jeffmerrick/typeframe/ps-85/software/images/nostromo-boot.png

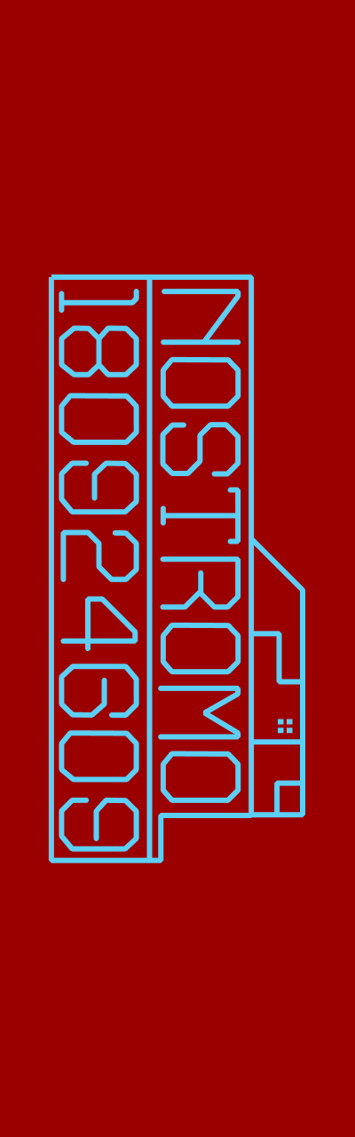
ps-85/software/images/nostromo-boot.png
