jeffmerrick/typeframe/px-88/software/images/typeframe-boot-simple.png

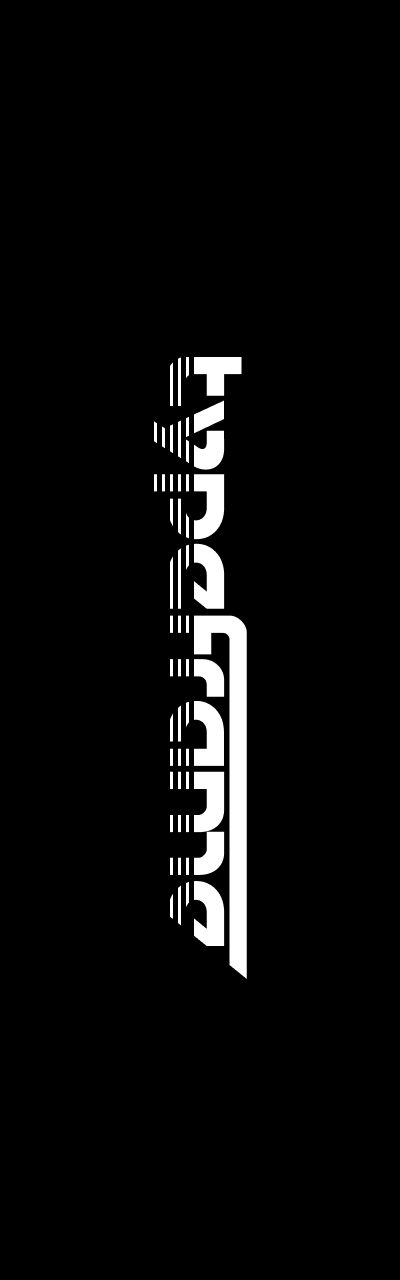
px-88/software/images/typeframe-boot-simple.png
