jeffmerrick/typeframe/website/docs/ps-85/img/typeframe-ps-85-02.jpg

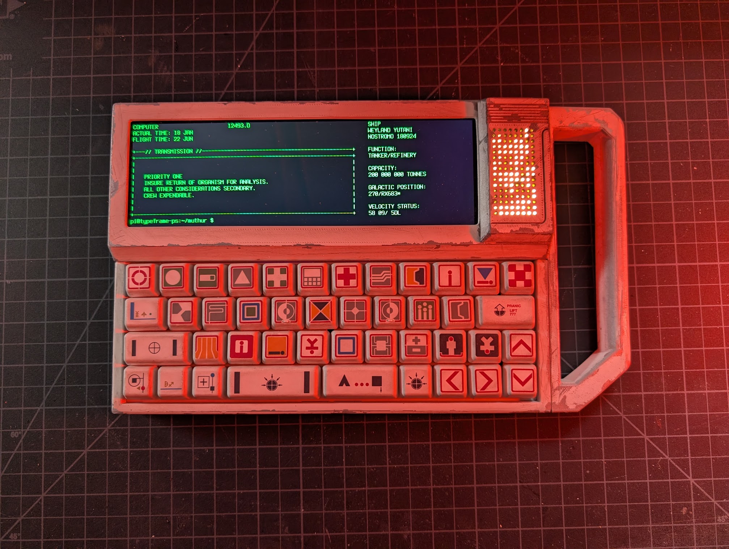
website/docs/ps-85/img/typeframe-ps-85-02.jpg
