jeffmerrick/typeframe/website/docs/ps-85/img/typeframe-ps-85-08.jpg

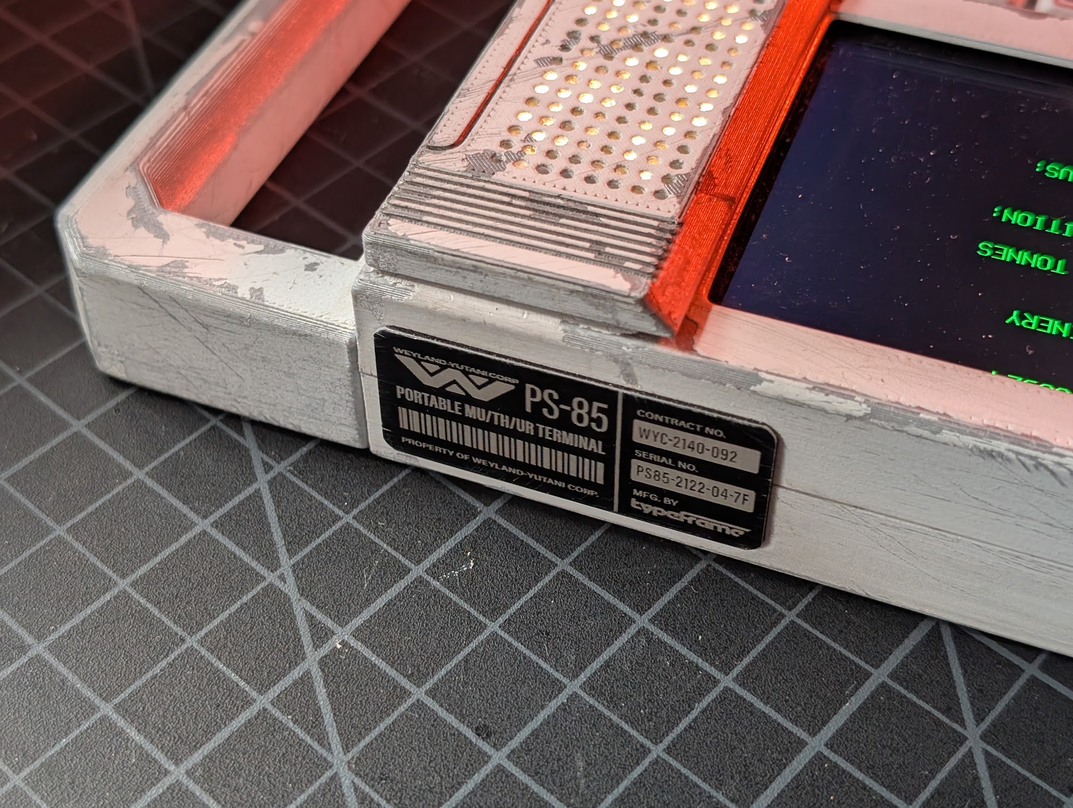
website/docs/ps-85/img/typeframe-ps-85-08.jpg
