jeffmerrick/typeframe/website/docs/px-88/img/typeframe-px-88-06.jpg

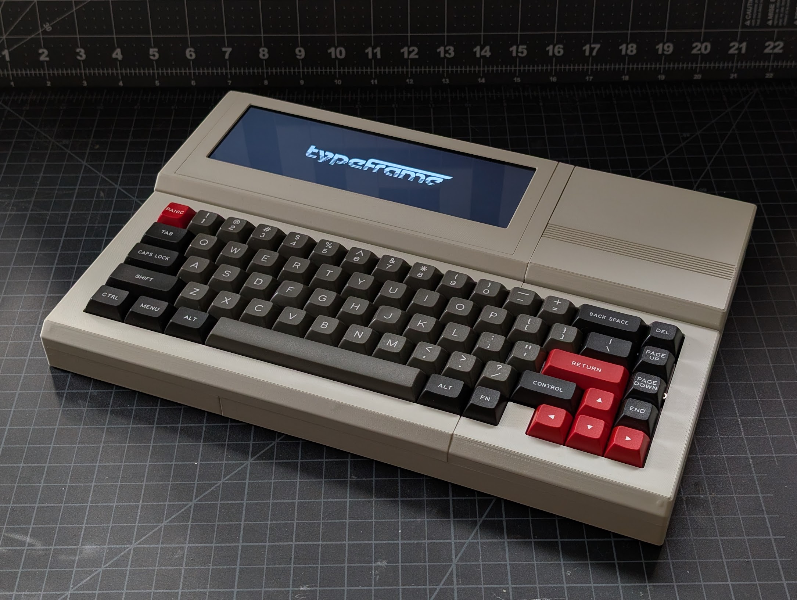
website/docs/px-88/img/typeframe-px-88-06.jpg
