jeffmerrick/typeframe/website/docs/px-88/img/typeframe-px-88-paul-2.jpg

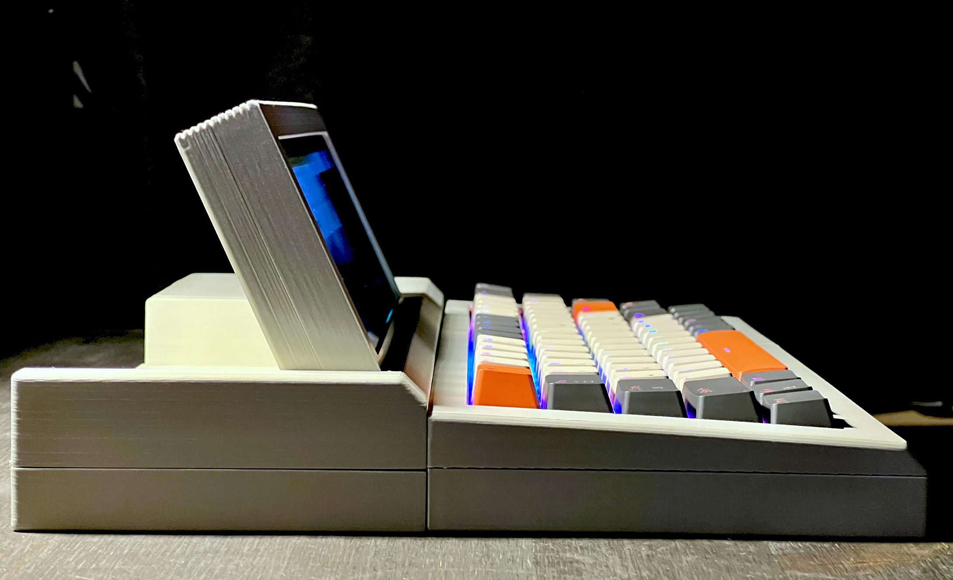
website/docs/px-88/img/typeframe-px-88-paul-2.jpg
