jeffmerrick/typeframe/website/docs/px-88/img/typeframe-px-88-paul-3.jpg

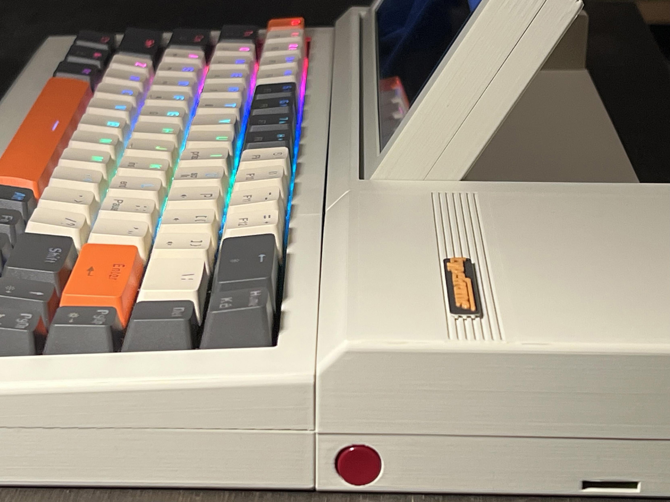
website/docs/px-88/img/typeframe-px-88-paul-3.jpg
