jeffmerrick/typeframe/website/src/pages/img/typeframe-ps-85-hero-simple.png

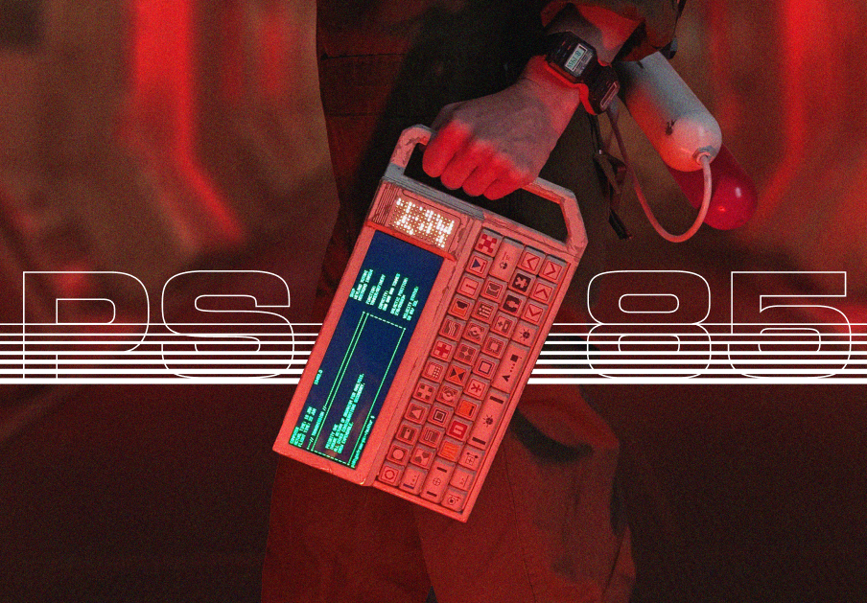
website/src/pages/img/typeframe-ps-85-hero-simple.png
