jeffmerrick/typeframe/website/src/pages/img/typeframe-ps-85-hero.png

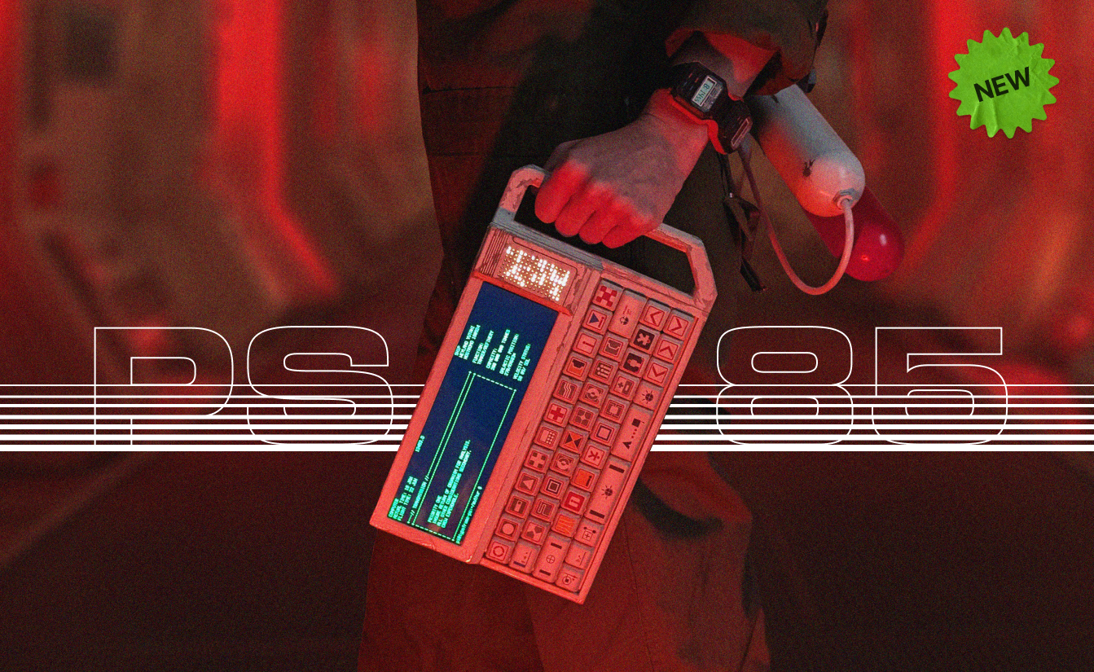
website/src/pages/img/typeframe-ps-85-hero.png
