jeffmerrick/typeframe/website/src/pages/img/typeframe-px-88-hero-simple.png

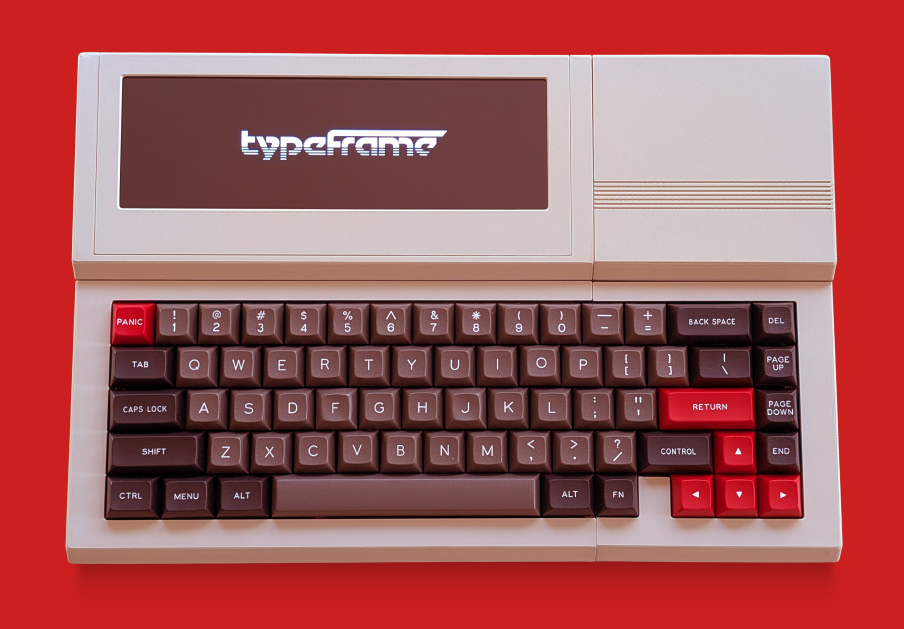
website/src/pages/img/typeframe-px-88-hero-simple.png
