jeffmerrick/typeframe/website/src/pages/img/typeframe-px-88-hero.png

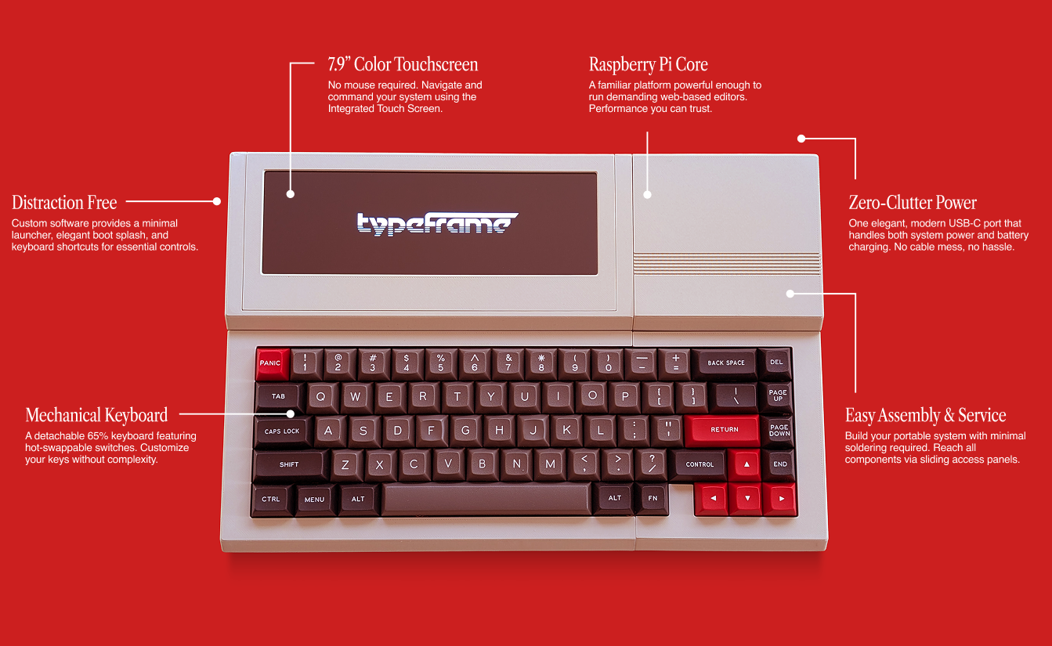
website/src/pages/img/typeframe-px-88-hero.png
