jeffmerrick/typeframe/px-88/hardware/print-files/tight-tolerances/STL/hinge_shaft_x2_0.05mm.stl

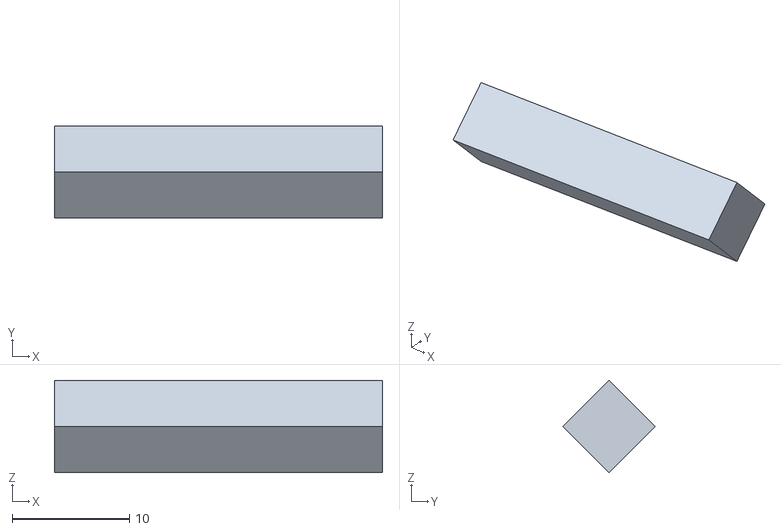
[picture p51: CAD file, 2025-11-28]
px-88/hardware/print-files/tight-tolerances/STL/hinge_shaft_x2_0.05mm.stl
28.0 x 7.86 x 7.86
