jeffmerrick/typeframe/ps-85/hardware/print-files/STL/keyboard_plate.stl

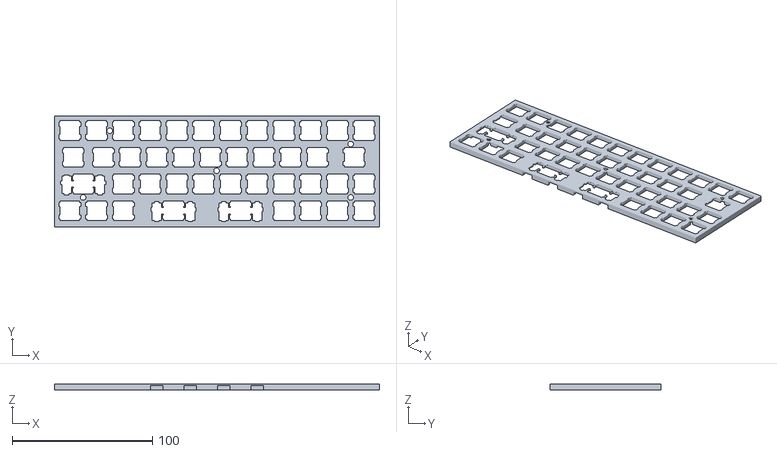
[picture p52: CAD file, 2026-01-20]
ps-85/hardware/print-files/STL/keyboard_plate.stl
231.4 x 78.8 x 4.40
