jeffmerrick/typeframe/px-88/hardware/print-files/loose-tolerances/STL/keyboard_case_top_right.stl

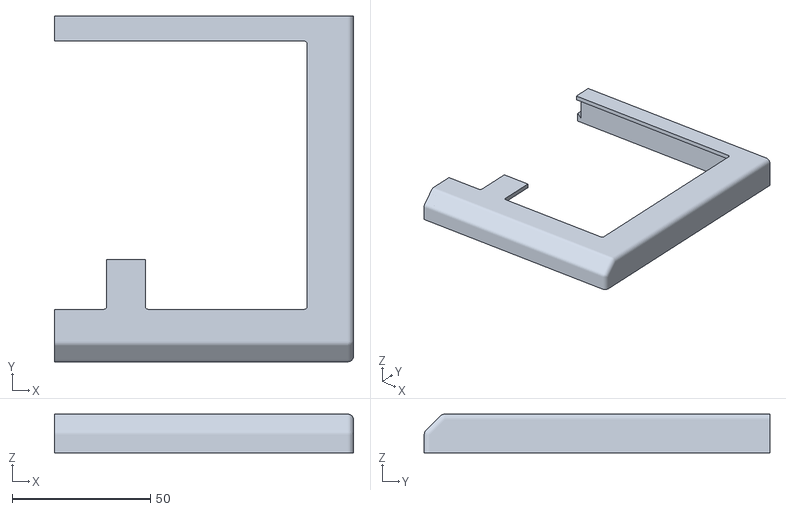
[picture p53: CAD file, 2025-12-03]
px-88/hardware/print-files/loose-tolerances/STL/keyboard_case_top_right.stl
108.1 x 125.0 x 14.0
