jeffmerrick/typeframe/px-88/hardware/print-files/tight-tolerances/3MF/keyboard_case.3mf

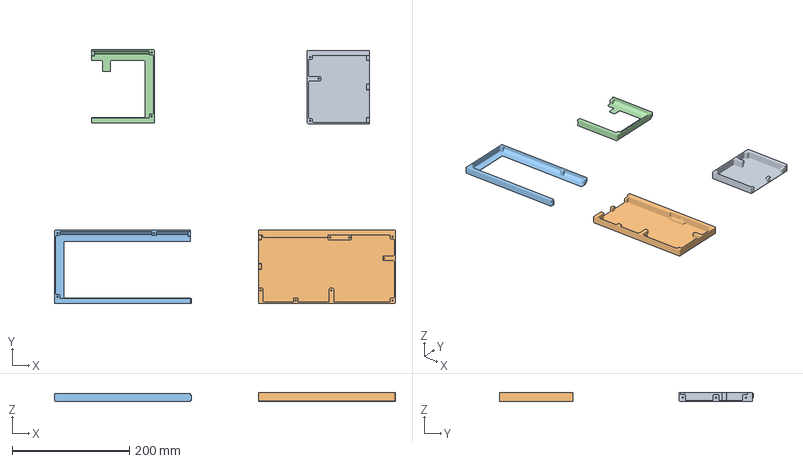
[picture p54: CAD file, 2025-11-03]
px-88/hardware/print-files/tight-tolerances/3MF/keyboard_case.3mf
581.8 x 432.9 x 16.0 mm
keyboard case bottom left
keyboard case bottom right
keyboard case top left
keyboard case top right
