jeffmerrick/typeframe/ps-85/hardware/print-files/STL/keyboard_top.stl

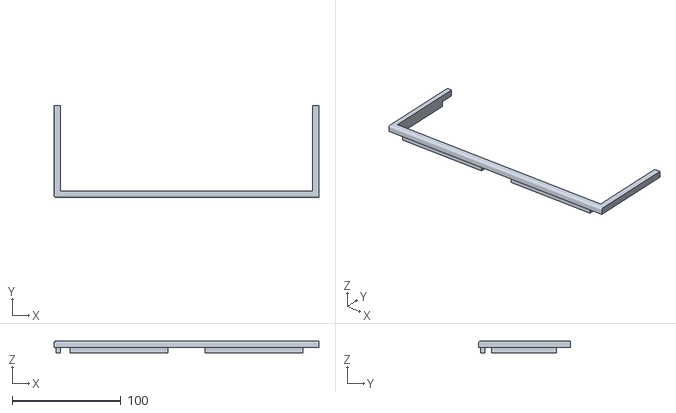
[picture p56: CAD file, 2026-01-20]
ps-85/hardware/print-files/STL/keyboard_top.stl
243.6 x 85.0 x 11.0
