jeffmerrick/typeframe/px-88/hardware/print-files/loose-tolerances/STL/keyboard_case_top_left.stl

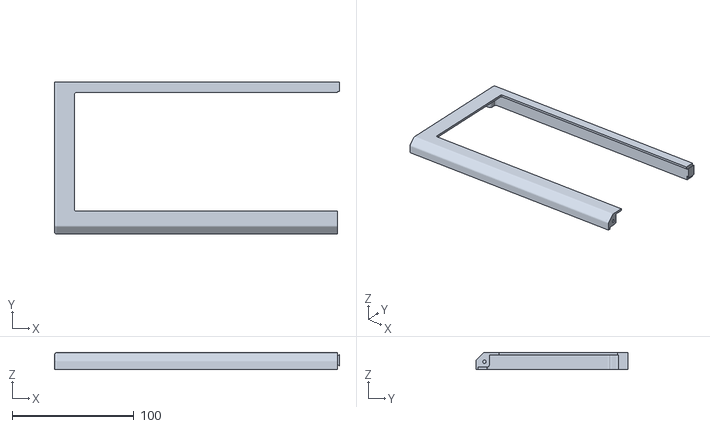
[picture p57: CAD file, 2025-12-03]
px-88/hardware/print-files/loose-tolerances/STL/keyboard_case_top_left.stl
233.6 x 125.0 x 14.0
