jeffmerrick/typeframe/px-88/hardware/print-files/tight-tolerances/STL/hinge_barrel_x2_0.15mm.stl

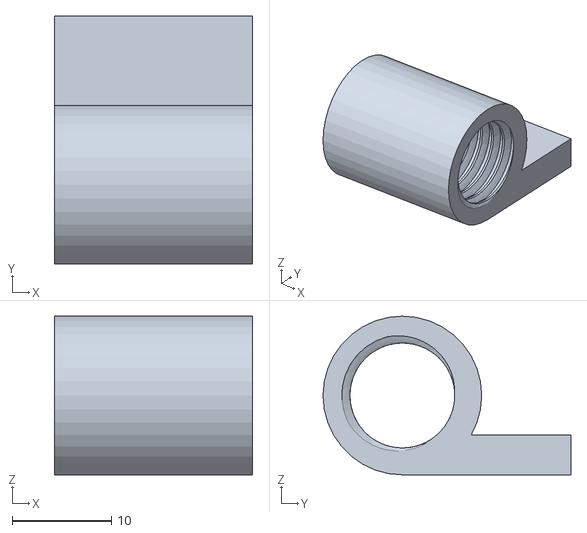
[picture p58: CAD file, 2025-11-28]
px-88/hardware/print-files/tight-tolerances/STL/hinge_barrel_x2_0.15mm.stl
20.0 x 25.0 x 16.0
