jeffmerrick/typeframe/ps-85/hardware/print-files/STL/handle.stl

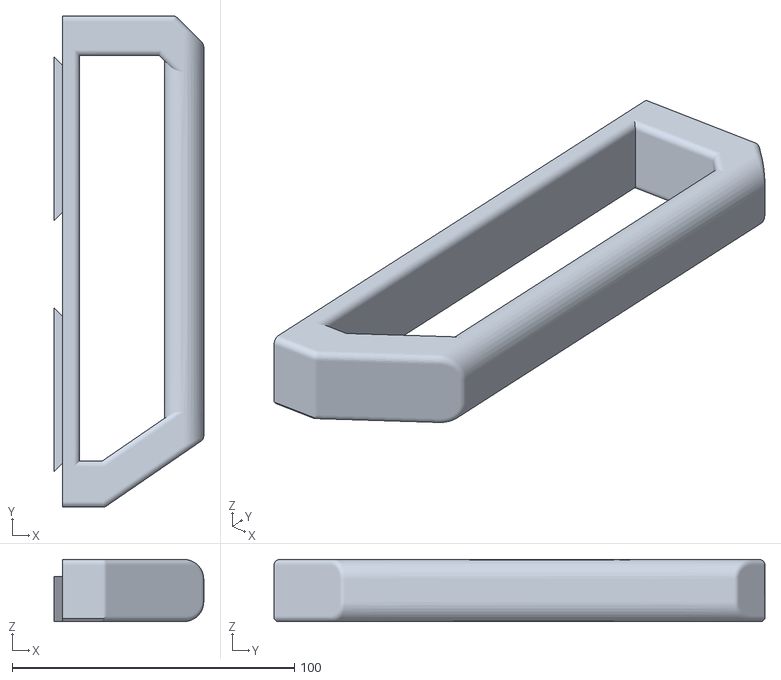
[picture p59: CAD file, 2026-01-20]
ps-85/hardware/print-files/STL/handle.stl
53.0 x 174.0 x 22.0
