jeffmerrick/typeframe/px-88/hardware/print-files/loose-tolerances/STL/screen_bottom.stl

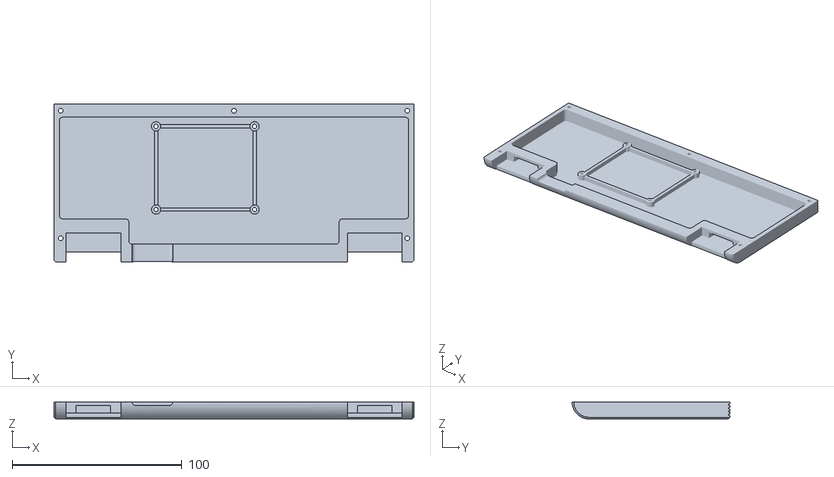
[picture p60: CAD file, 2025-12-03]
px-88/hardware/print-files/loose-tolerances/STL/screen_bottom.stl
212.0 x 93.0 x 10.0
