jeffmerrick/typeframe/px-88/hardware/print-files/tight-tolerances/STL/hinge_slider_x2.stl

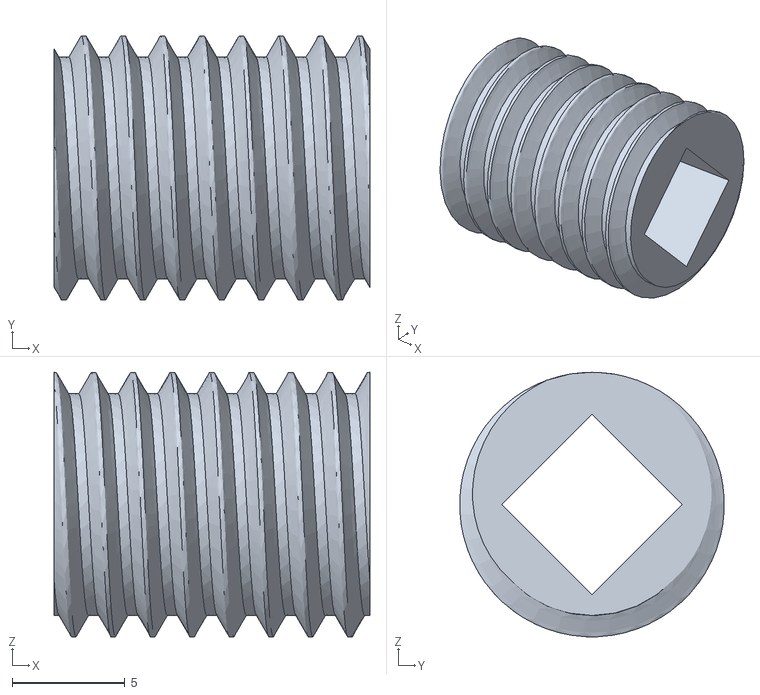
[picture p61: CAD file, 2025-11-28]
px-88/hardware/print-files/tight-tolerances/STL/hinge_slider_x2.stl
14.0 x 11.7 x 11.7
