jeffmerrick/typeframe/ps-85/hardware/print-files/STL/screen_top.stl

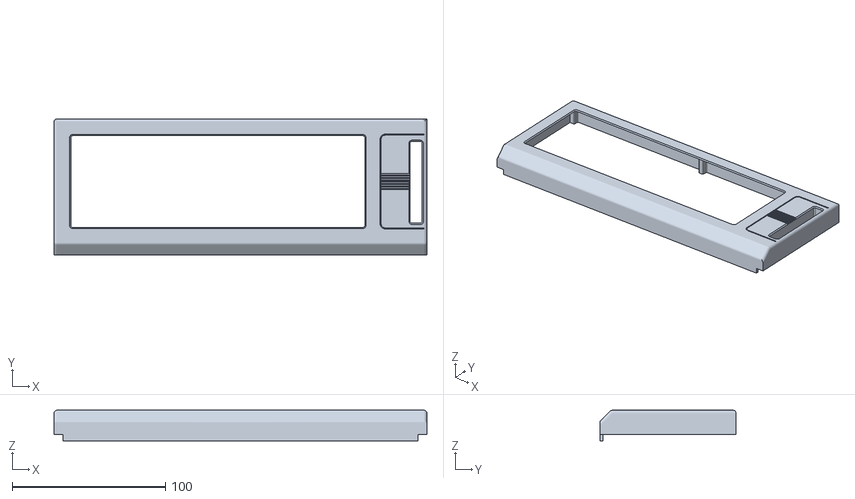
[picture p62: CAD file, 2026-01-20]
ps-85/hardware/print-files/STL/screen_top.stl
243.6 x 89.0 x 20.0
