jeffmerrick/typeframe/px-88/hardware/print-files/loose-tolerances/STL/case_lid.stl

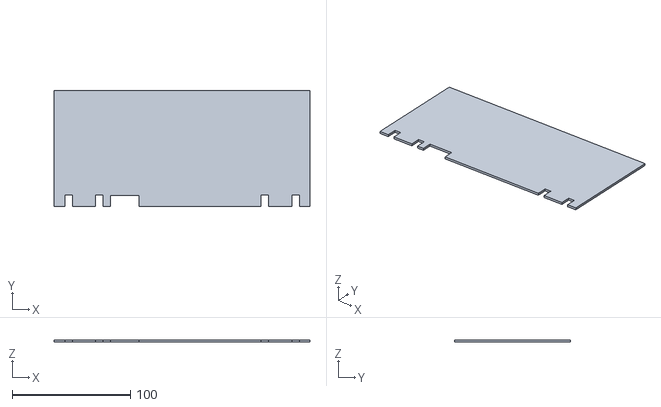
[picture p63: CAD file, 2025-12-03]
px-88/hardware/print-files/loose-tolerances/STL/case_lid.stl
216.1 x 97.9 x 2.00
