jeffmerrick/typeframe/px-88/hardware/print-files/loose-tolerances/STL/keyboard_case_bottom_right.stl

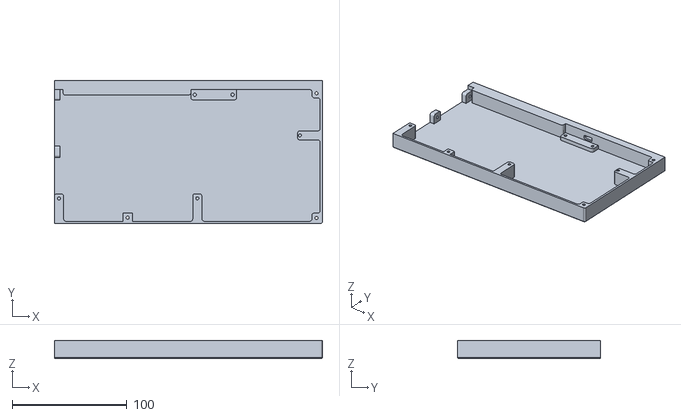
[picture p64: CAD file, 2025-12-03]
px-88/hardware/print-files/loose-tolerances/STL/keyboard_case_bottom_right.stl
234.0 x 125.0 x 16.0
