jeffmerrick/typeframe/px-88/hardware/print-files/loose-tolerances/STL/screen_top.stl

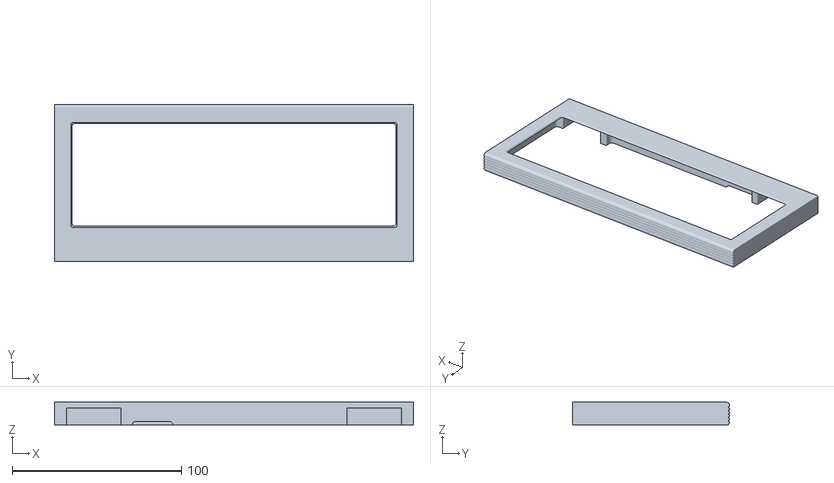
[picture p65: CAD file, 2025-12-03]
px-88/hardware/print-files/loose-tolerances/STL/screen_top.stl
212.0 x 93.0 x 13.4
