jeffmerrick/typeframe/px-88/hardware/print-files/tight-tolerances/STL/hinge_cap_right_x2.stl

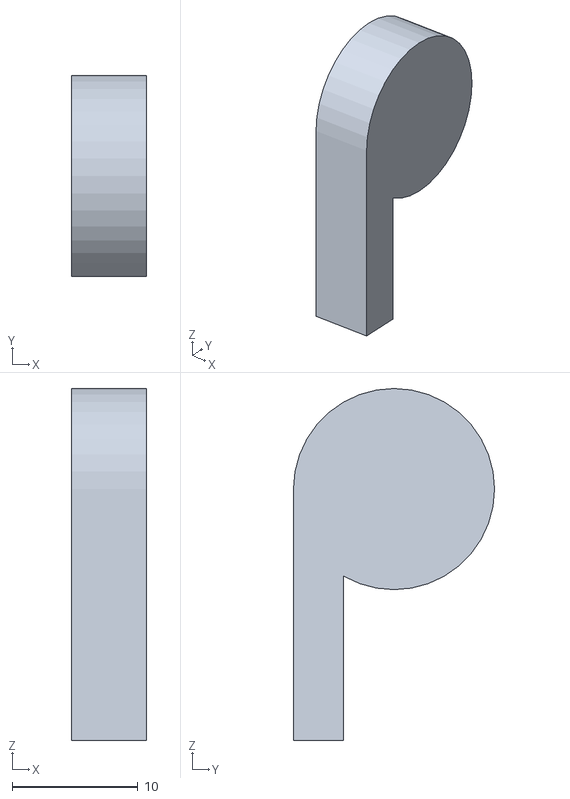
[picture p66: CAD file, 2025-11-03]
px-88/hardware/print-files/tight-tolerances/STL/hinge_cap_right_x2.stl
6.00 x 16.0 x 28.0
