jeffmerrick/typeframe/px-88/hardware/print-files/loose-tolerances/STL/screen_border.stl

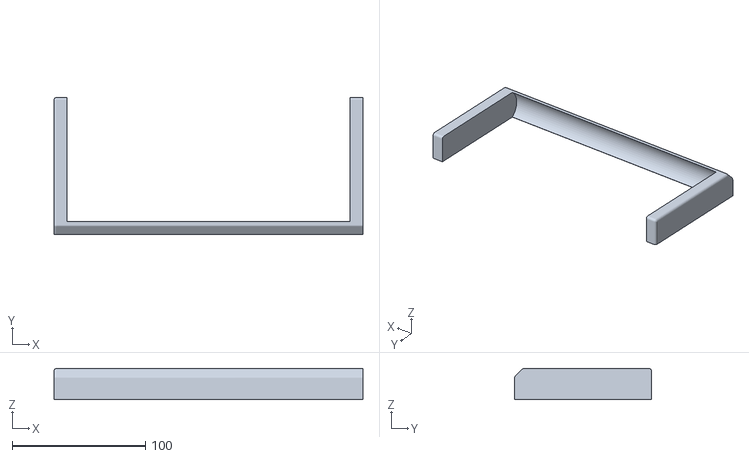
[picture p67: CAD file, 2025-12-03]
px-88/hardware/print-files/loose-tolerances/STL/screen_border.stl
232.0 x 103.0 x 23.4
