jeffmerrick/typeframe/px-88/hardware/print-files/tight-tolerances/STL/badge_bottom.stl

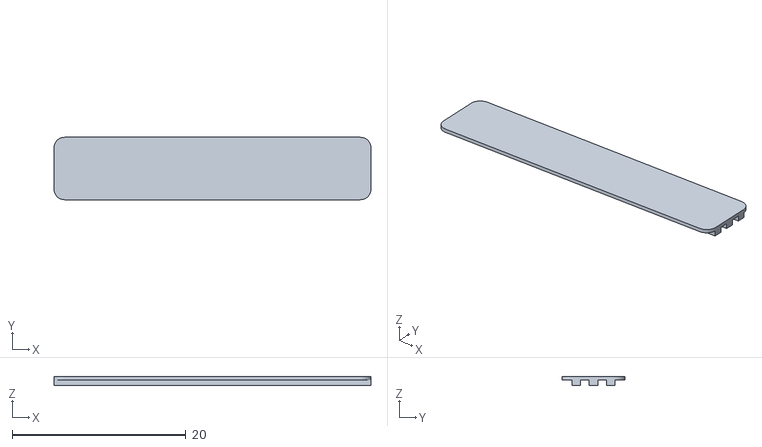
[picture p68: CAD file, 2025-11-03]
px-88/hardware/print-files/tight-tolerances/STL/badge_bottom.stl
36.5 x 7.20 x 1.00
