jeffmerrick/typeframe/px-88/hardware/print-files/tight-tolerances/STL/screen_border.stl

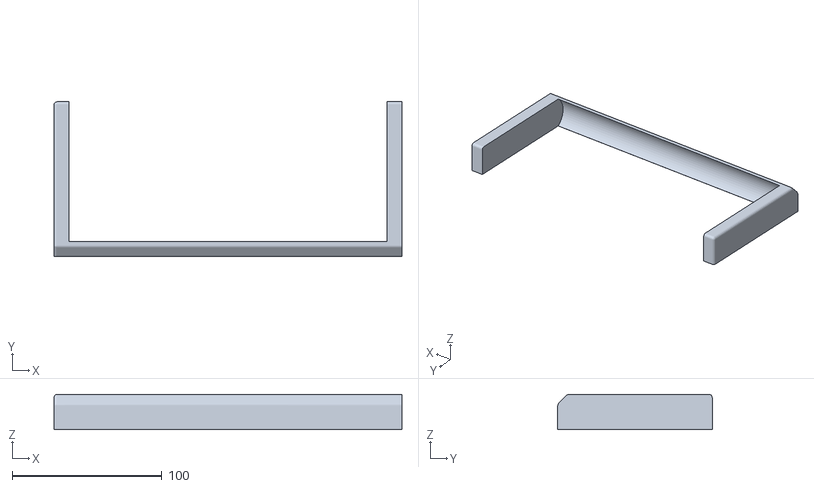
[picture p69: CAD file, 2025-11-03]
px-88/hardware/print-files/tight-tolerances/STL/screen_border.stl
232.0 x 103.0 x 23.4
