jeffmerrick/typeframe/px-88/hardware/print-files/tight-tolerances/STL/side_top.stl

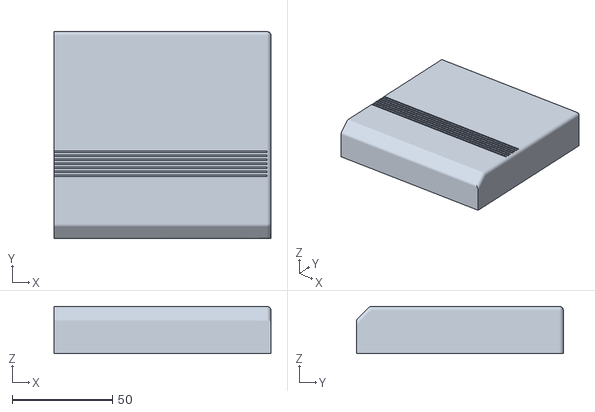
[picture p71: CAD file, 2025-11-03]
px-88/hardware/print-files/tight-tolerances/STL/side_top.stl
108.0 x 103.0 x 23.4
