jeffmerrick/typeframe/website/docs/px-88/assembly/img/hinge-assembly-02.jpg

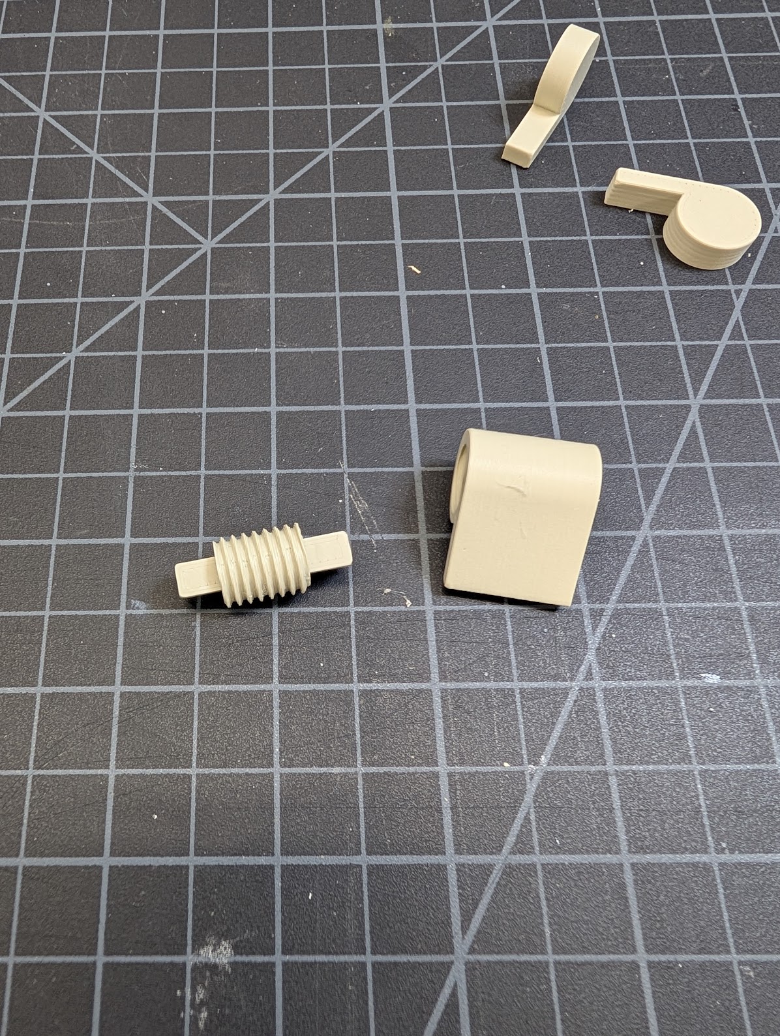
website/docs/px-88/assembly/img/hinge-assembly-02.jpg
