jeffmerrick/typeframe/website/docs/px-88/assembly/img/soldering-power-switch-02.jpg

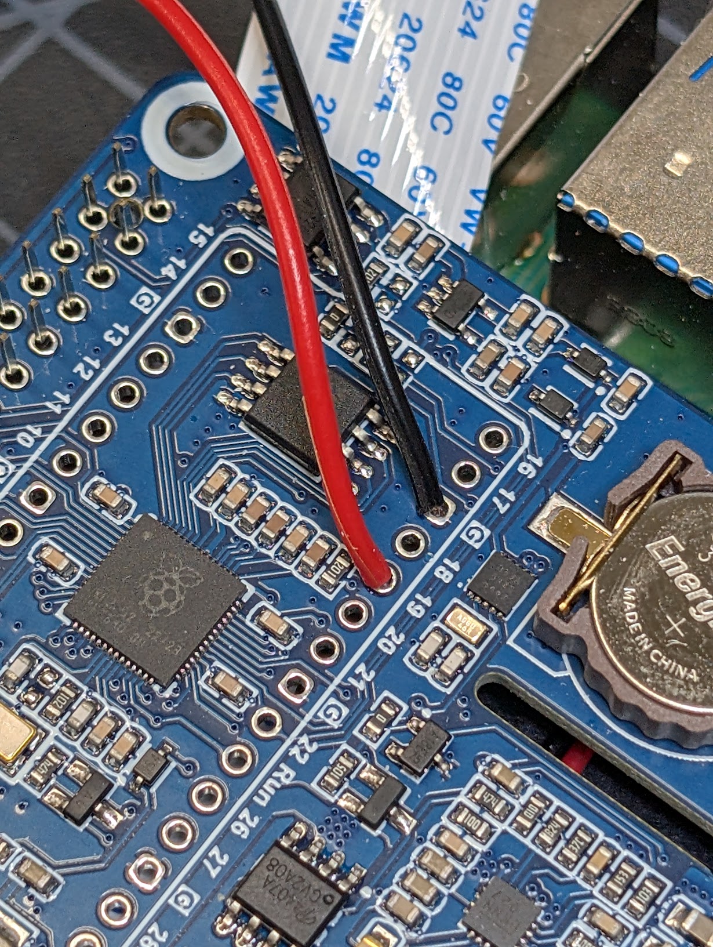
website/docs/px-88/assembly/img/soldering-power-switch-02.jpg
